Tinkerforge/industrial-digital-out-4-v2-bricklet/software/src/communication.c

/* industrial-digital-out-4-v2-bricklet
 * Copyright (C) 2018 Ishraq Ibne Ashraf <ishraq@tinkerforge.com>
 * Copyright (C) 2018-2020 Olaf Lüke <olaf@tinkerforge.com>
 *
 * communication.c: TFP protocol message handling
 *
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
 * You should have received a copy of the GNU Lesser General Public
 * License along with this library; if not, write to the
 * Free Software Foundation, Inc., 59 Temple Place - Suite 330,
 * Boston, MA 02111-1307, USA.
 */

#include "communication.h"

#include "bricklib2/utility/communication_callback.h"
#include "bricklib2/protocols/tfp/tfp.h"
#include "bricklib2/logging/logging.h"

#include "ido4.h"
#include "wiegand.h"

extern const uint8_t ido4_channel_pin[];
extern XMC_GPIO_PORT_t *const ido4_channel_port[];

BootloaderHandleMessageResponse handle_message(const void *message, void *response) {
	switch(tfp_get_fid_from_message(message)) {
		case FID_SET_VALUE: return set_value(message);
		case FID_GET_VALUE: return get_value(message, response);
		case FID_SET_SELECTED_VALUE: return set_selected_value(message);
		case FID_SET_MONOFLOP: return set_monoflop(message);
		case FID_GET_MONOFLOP: return get_monoflop(message, response);
		case FID_SET_CHANNEL_LED_CONFIG: return set_channel_led_config(message);
		case FID_GET_CHANNEL_LED_CONFIG: return get_channel_led_config(message, response);
		case FID_SET_PWM_CONFIGURATION: return set_pwm_configuration(message);
		case FID_GET_PWM_CONFIGURATION: return get_pwm_configuration(message, response);
		case FID_WRITE_WIEGAND_DATA_LOW_LEVEL: return write_wiegand_data_low_level(message);
		case FID_GET_WIEGAND_STATE: return get_wiegand_state(message, response);
		default: return HANDLE_MESSAGE_RESPONSE_NOT_SUPPORTED;
	}
}

BootloaderHandleMessageResponse set_value(const SetValue *data) {
	logd("[+] IDO4-V2: set_value()\n\r");

	for(uint8_t i = 0; i < IDO4_CHANNEL_NUM; i++) {
		// abort potentially pending monoflop
		ido4.channels[i].monoflop.time_start = 0;
		ido4.channels[i].monoflop.time_remaining = 0;
		ido4.channels[i].monoflop.running = false;

		if(data->value & (1 << i)) {
			ido4.channels[i].value = true;
			XMC_GPIO_SetOutputLow(ido4_channel_port[i], ido4_channel_pin[i]);
		}
		else {
			ido4.channels[i].value = false;
			XMC_GPIO_SetOutputHigh(ido4_channel_port[i], ido4_channel_pin[i]);
		}
	}

	return HANDLE_MESSAGE_RESPONSE_EMPTY;
}

BootloaderHandleMessageResponse get_value(const GetValue *data, GetValue_Response *response) {
	logd("[+] IDO4-V2: get_value()\n\r");

	uint8_t bit_encoded_values = 0;
	response->header.length = sizeof(GetValue_Response);

	for(uint8_t i = 0; i < IDO4_CHANNEL_NUM; i++) {
		if(ido4.channels[i].value) {
			bit_encoded_values |= (1 << i);
		}
		else {
			bit_encoded_values &= ~(1 << i);
		}
	}

	response->value = bit_encoded_values;

	return HANDLE_MESSAGE_RESPONSE_NEW_MESSAGE;
}

BootloaderHandleMessageResponse set_selected_value(const SetSelectedValue *data) {
	logd("[+] IDO4-V2: set_selected_value()\n\r");

	if(data->channel > IDO4_CHANNEL_NUM - 1) {
		return HANDLE_MESSAGE_RESPONSE_INVALID_PARAMETER;
	}

	// Reset PWM
	ido4_pwm_stop(data->channel);

	// abort potentially pending monoflop
	ido4.channels[data->channel].monoflop.time_start = 0;
	ido4.channels[data->channel].monoflop.time_remaining = 0;
	ido4.channels[data->channel].monoflop.running = false;

	ido4.channels[data->channel].value = data->value;

	if(ido4.channels[data->channel].value) {
		XMC_GPIO_SetOutputLow(ido4_channel_port[data->channel], ido4_channel_pin[data->channel]);
	}
	else {
		XMC_GPIO_SetOutputHigh(ido4_channel_port[data->channel], ido4_channel_pin[data->channel]);
	}

	return HANDLE_MESSAGE_RESPONSE_EMPTY;
}

BootloaderHandleMessageResponse set_monoflop(const SetMonoflop *data) {
	logd("[+] IDO4-V2: set_monoflop()\n\r");

	if(data->channel > IDO4_CHANNEL_NUM - 1) {
		return HANDLE_MESSAGE_RESPONSE_INVALID_PARAMETER;
	}

	// Reset PWM
	ido4_pwm_stop(data->channel);

	ido4.channels[data->channel].value = data->value;
	ido4.channels[data->channel].monoflop.time = data->time;
	ido4.channels[data->channel].monoflop.time_remaining = data->time;
	ido4.channels[data->channel].monoflop.running = true;

	if(ido4.channels[data->channel].value) {
		XMC_GPIO_SetOutputLow(ido4_channel_port[data->channel], ido4_channel_pin[data->channel]);
	}
	else {
		XMC_GPIO_SetOutputHigh(ido4_channel_port[data->channel], ido4_channel_pin[data->channel]);
	}

	ido4.channels[data->channel].monoflop.time_start = system_timer_get_ms();

	return HANDLE_MESSAGE_RESPONSE_EMPTY;
}

BootloaderHandleMessageResponse get_monoflop(const GetMonoflop *data, GetMonoflop_Response *response) {
	logd("[+] IDO4-V2: get_monoflop()\n\r");

	response->header.length = sizeof(GetMonoflop_Response);

	if(data->channel > IDO4_CHANNEL_NUM - 1) {
		return HANDLE_MESSAGE_RESPONSE_INVALID_PARAMETER;
	}

	response->time = ido4.channels[data->channel].monoflop.time;
	response->value = ido4.channels[data->channel].value;
	response->time_remaining = ido4.channels[data->channel].monoflop.time_remaining;

	return HANDLE_MESSAGE_RESPONSE_NEW_MESSAGE;
}

BootloaderHandleMessageResponse set_channel_led_config(const SetChannelLEDConfig *data) {
	if(data->channel > IDO4_CHANNEL_NUM - 1) {
		return HANDLE_MESSAGE_RESPONSE_INVALID_PARAMETER;
	}

	ido4.channels[data->channel].status_led.config = data->config;

	return HANDLE_MESSAGE_RESPONSE_EMPTY;
}

BootloaderHandleMessageResponse get_channel_led_config(const GetChannelLEDConfig *data, GetChannelLEDConfig_Response *response) {
	response->header.length = sizeof(GetChannelLEDConfig_Response);

	if(data->channel > IDO4_CHANNEL_NUM - 1) {
		return HANDLE_MESSAGE_RESPONSE_INVALID_PARAMETER;
	}

	response->config = ido4.channels[data->channel].status_led.config;

	return HANDLE_MESSAGE_RESPONSE_NEW_MESSAGE;
}

BootloaderHandleMessageResponse set_pwm_configuration(const SetPWMConfiguration *data) {
	if(data->channel >= IDO4_CHANNEL_NUM) {
		return HANDLE_MESSAGE_RESPONSE_INVALID_PARAMETER;
	}

	// Reset monoflop
	ido4.channels[data->channel].monoflop.time_start = 0;
	ido4.channels[data->channel].monoflop.time_remaining = 0;
	ido4.channels[data->channel].monoflop.running = false;

	ido4_pwm_update(data->channel, data->frequency, data->duty_cycle);

	return HANDLE_MESSAGE_RESPONSE_EMPTY;
}

BootloaderHandleMessageResponse get_pwm_configuration(const GetPWMConfiguration *data, GetPWMConfiguration_Response *response) {
	if(data->channel >= IDO4_CHANNEL_NUM) {
		return HANDLE_MESSAGE_RESPONSE_INVALID_PARAMETER;
	}

	response->header.length = sizeof(GetPWMConfiguration_Response);
	response->duty_cycle    = ido4.channels[data->channel].pwm.duty_cycle;
	response->frequency     = ido4.channels[data->channel].pwm.frequency;

	return HANDLE_MESSAGE_RESPONSE_NEW_MESSAGE;
}

BootloaderHandleMessageResponse write_wiegand_data_low_level(const WriteWiegandDataLowLevel *data) {
	if(data->data_length > 256) {
		return HANDLE_MESSAGE_RESPONSE_INVALID_PARAMETER;
	}

	// Reset monoflop for channel 0 and 1
	ido4.channels[0].monoflop.time_start     = 0;
	ido4.channels[1].monoflop.time_start     = 0;
	ido4.channels[0].monoflop.time_remaining = 0;
	ido4.channels[1].monoflop.time_start     = 0;
	ido4.channels[0].monoflop.running        = false;
	ido4.channels[1].monoflop.running        = false;

	memcpy(wiegand.data, data->data_data, 32);
	wiegand.data_length = data->data_length;
	wiegand.data_index  = 0;
	wiegand.last_time   = 0;

	return HANDLE_MESSAGE_RESPONSE_EMPTY;
}

BootloaderHandleMessageResponse get_wiegand_state(const GetWiegandState *data, GetWiegandState_Response *response) {
	response->header.length = sizeof(GetWiegandState_Response);
	if(wiegand.data_length > 0) {
		response->wiegand_state = INDUSTRIAL_DIGITAL_OUT_4_V2_WIEGAND_STATE_BUSY;
	} else {
		response->wiegand_state = INDUSTRIAL_DIGITAL_OUT_4_V2_WIEGAND_STATE_IDLE;
	}

	return HANDLE_MESSAGE_RESPONSE_NEW_MESSAGE;
}


bool handle_monoflop_done_callback(void) {
	static bool is_buffered = false;
	static MonoflopDone_Callback cb;

	if(!is_buffered) {
		if(ringbuffer_is_empty(&ido4.monoflop_cb_rb)) {
			// Nothing to send
			return false;
		}

		tfp_make_default_header(&cb.header,
		                        bootloader_get_uid(),
		                        sizeof(MonoflopDone_Callback),
		                        FID_CALLBACK_MONOFLOP_DONE);

		ringbuffer_get(&ido4.monoflop_cb_rb, &cb.channel);
		ringbuffer_get(&ido4.monoflop_cb_rb, (uint8_t *)&cb.value);
	}

	if(bootloader_spitfp_is_send_possible(&bootloader_status.st)) {
		bootloader_spitfp_send_ack_and_message(&bootloader_status,
		                                       (uint8_t*)&cb,
		                                       sizeof(MonoflopDone_Callback));

		is_buffered = false;

		return true;
	}
	else {
		is_buffered = true;
	}

	return false;
}

bool handle_wiegand_done_callback(void) {
	static bool is_buffered = false;
	static WiegandDone_Callback cb;

	if(!is_buffered) {
		if(!wiegand.done) {
			return false;
		}

		tfp_make_default_header(&cb.header, bootloader_get_uid(), sizeof(WiegandDone_Callback), FID_CALLBACK_WIEGAND_DONE);
		wiegand.done = false;
	}

	if(bootloader_spitfp_is_send_possible(&bootloader_status.st)) {
		bootloader_spitfp_send_ack_and_message(&bootloader_status, (uint8_t*)&cb, sizeof(WiegandDone_Callback));
		is_buffered = false;
		return true;
	} else {
		is_buffered = true;
	}

	return false;
}

void communication_tick(void) {
	communication_callback_tick();
}

void communication_init(void) {
	communication_callback_init();
}
